Lekipon/ASTRA515/doc/img/astra515_01.JPG

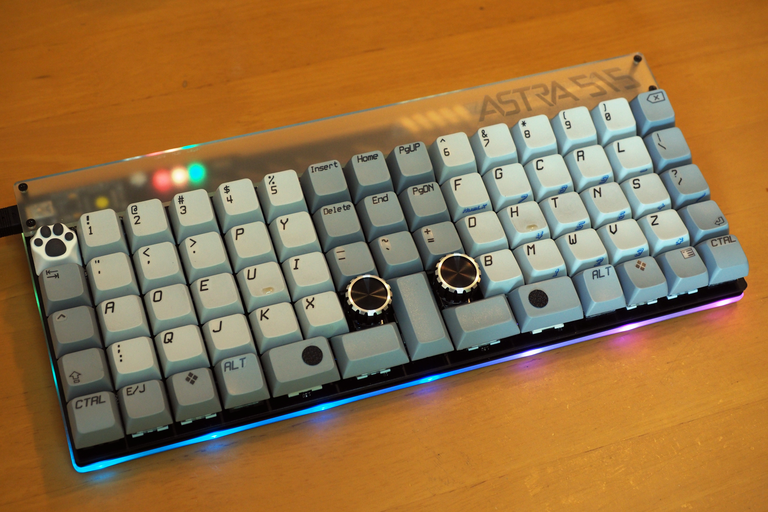
doc/img/astra515_01.JPG
